jina0924/Plantinum_vol2/Docs/Develop_log_server.md

# 서버 개발 일지

### 2022-08-05

##### [BE] 배포서버 구축 테스트
- 더미 장고 파일을 uwsgi를 사용해서 연결 확인
- 실제 어느정도 구현된 파일은 아직 불가능
    - 장고 하나로 했을 때는 연결되지만 프론트와 연결했을 때에는 되지 않는 문제 발생
    - 두가지 가설 : 포트 번호가 열려있지 않은 것 vs 가상환경
    - localhost:8000 으로 연결이 안된다는 에러메세지 => 장고 runserver 도 안되긴함
    - 프론트에 연결된 주소도 한번 봐야함
    - 다음에 포트번호 상황 여쭈어보기
    - 정안되면 Gunicorn 알아보기
