jina0924/Plantinum_vol2/Docs/[A109] 중간발표.pdf

### 서울 1반 A109

김유민 문요성 이지수 임진경 정진아

# Plantinum

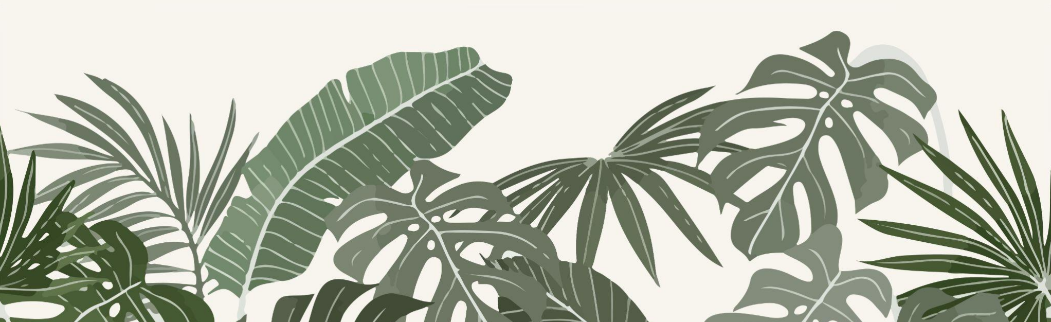
[picture p21: figure]

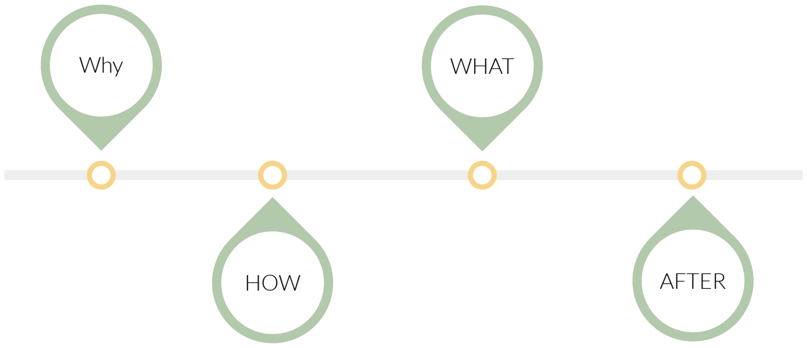
[picture p22: figure]
Why; HOW; WHAT; AFTER

HOW

WHAT

WHY

# CONTENTS

AFTER

# Why?

# WHY?

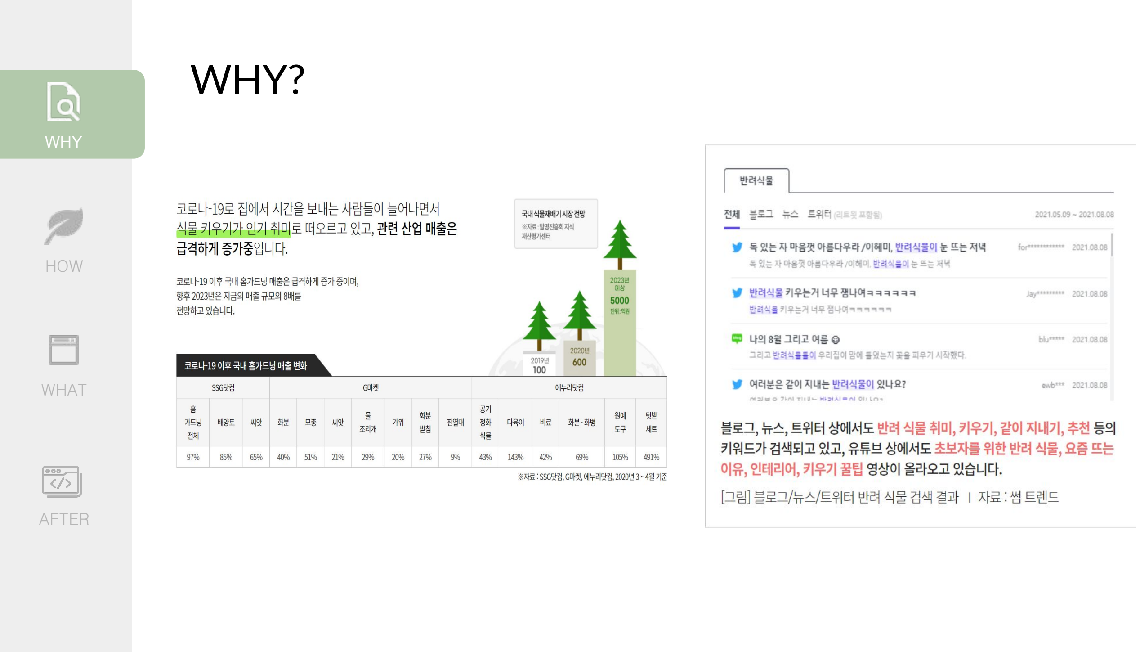
[picture p23: page 4]

WHY

HOW

WHAT

AFTER

# How?

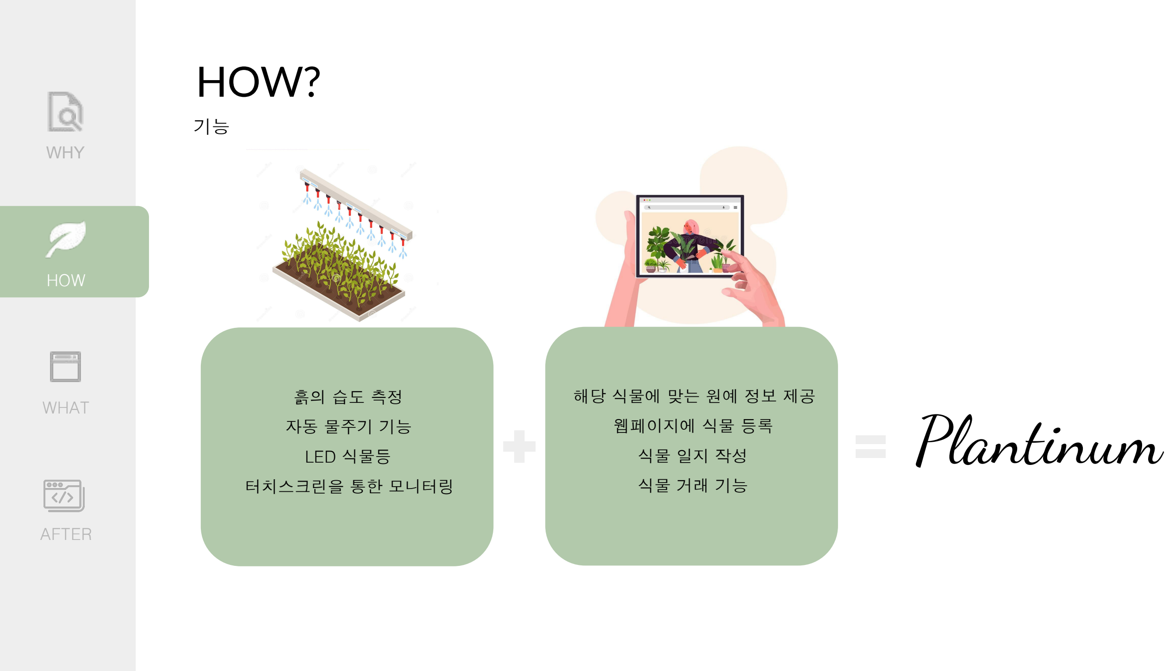
[picture p24: figure]
HOW; HOW?; 자동 물주기 기능; LED 식물등; 터치스크린을 통한 모니터링; 해당 식물에 맞는 원예 정보 제공; 웹페이지에 식물 등록; WHAT; WHY; AFTER; Plantinum

# What?

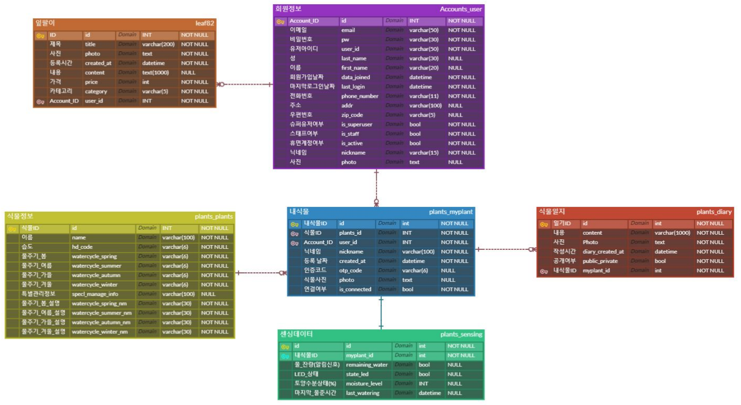
[picture p25: figure]

WHAT

# WHAT

HOW

WHY

AFTER

# WHAT

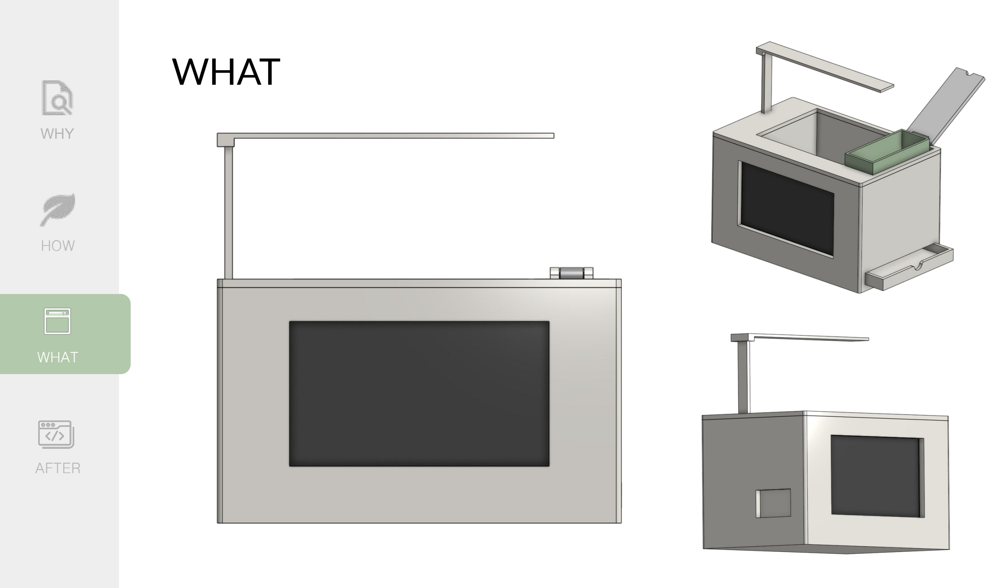
[picture p26: page 9]

WHAT

HOW

WHY

AFTER

## 신규 등록

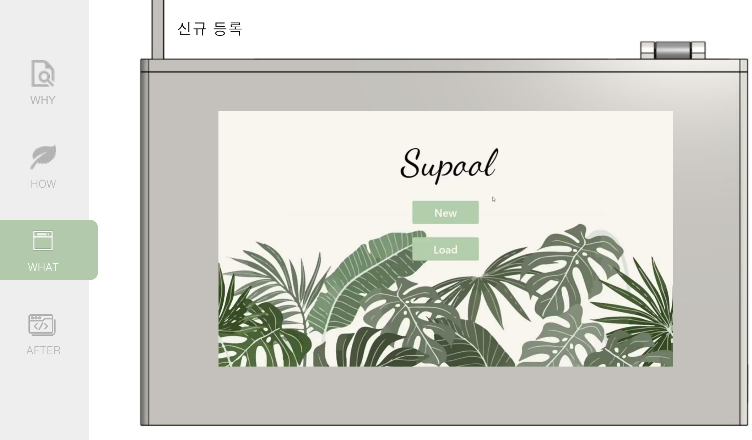
[picture p27: page 10]

WHAT

HOW

WHY

AFTER

## 기존정보 불러오기

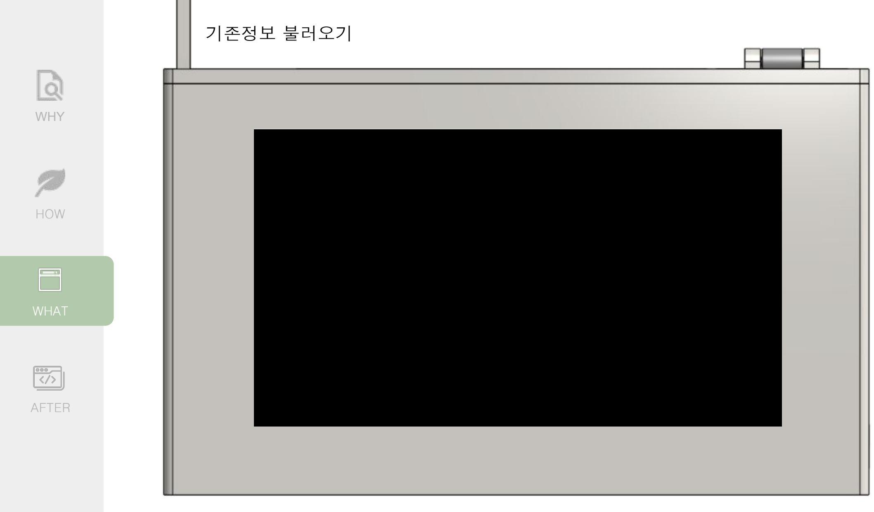
[picture p28: page 11]

WHAT

HOW

WHY

AFTER

# WHAT

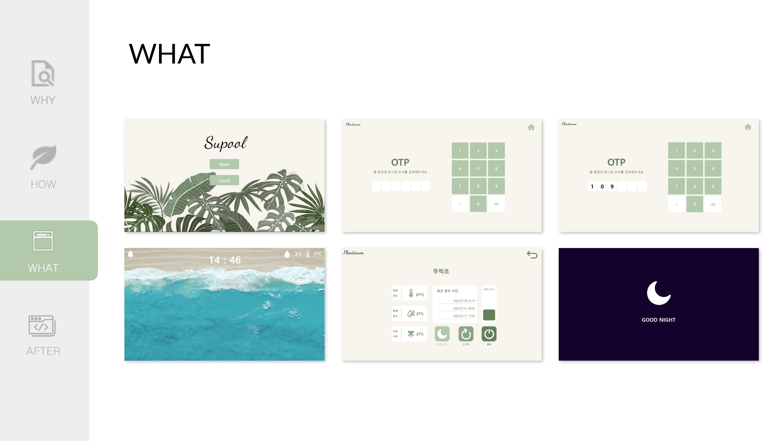
[picture p29: page 12]

WHAT

HOW

WHY

AFTER

# WHAT

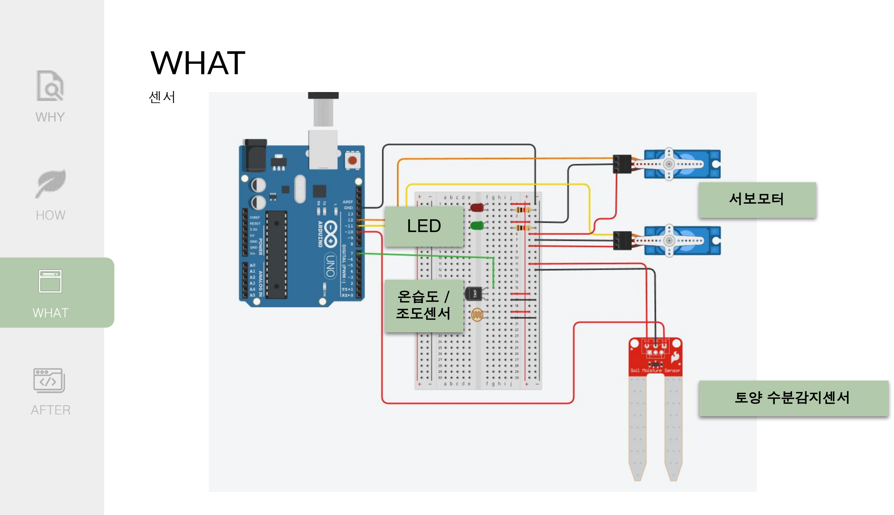
[picture p30: page 13]

센서

서보모터

토양 수분감지센서

## LED

온습도 /
WHAT | 조도센서

HOW

WHY

AFTER

# WHAT

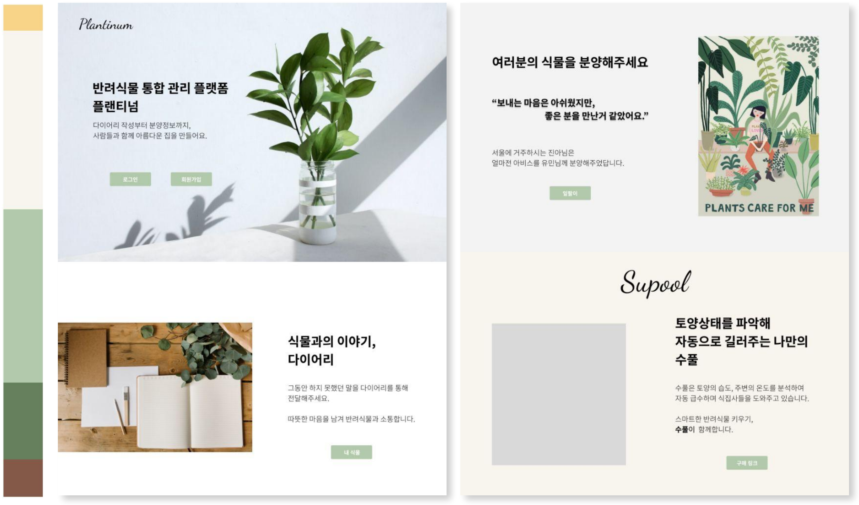
[picture p31: figure]

WHAT

HOW

WHY

AFTER

# WHAT

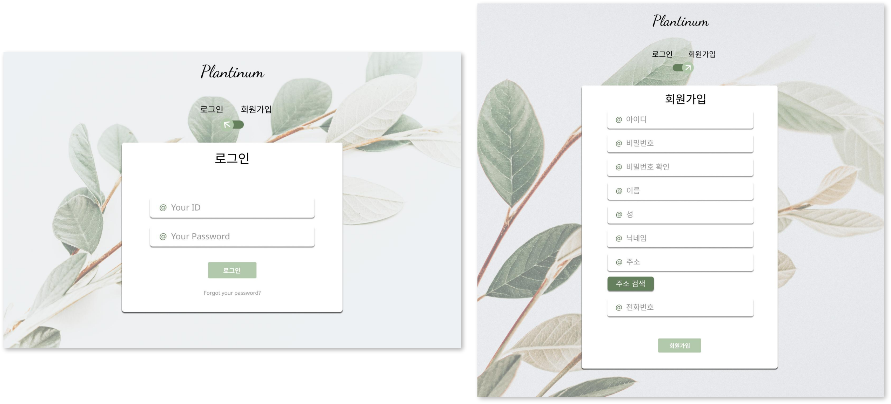
[picture p32: figure]

WHAT

HOW

WHY

AFTER

# WHAT

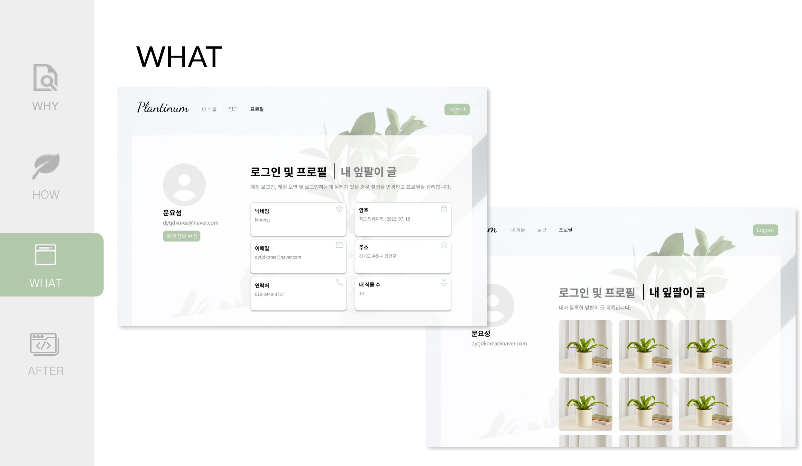
[picture p33: page 16]

WHAT

HOW

WHY

AFTER

# WHAT

WHAT

HOW

WHY

AFTER

## (시연 영상)

# After?

# AFTER

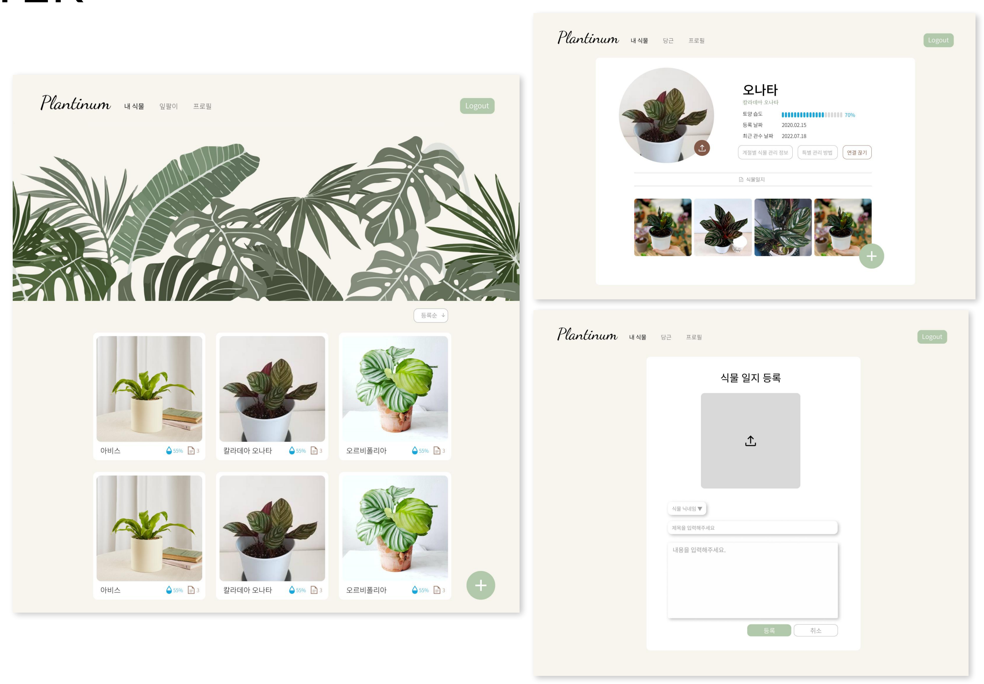
[picture p34: figure]

HOW

WHY

AFTER

WHAT

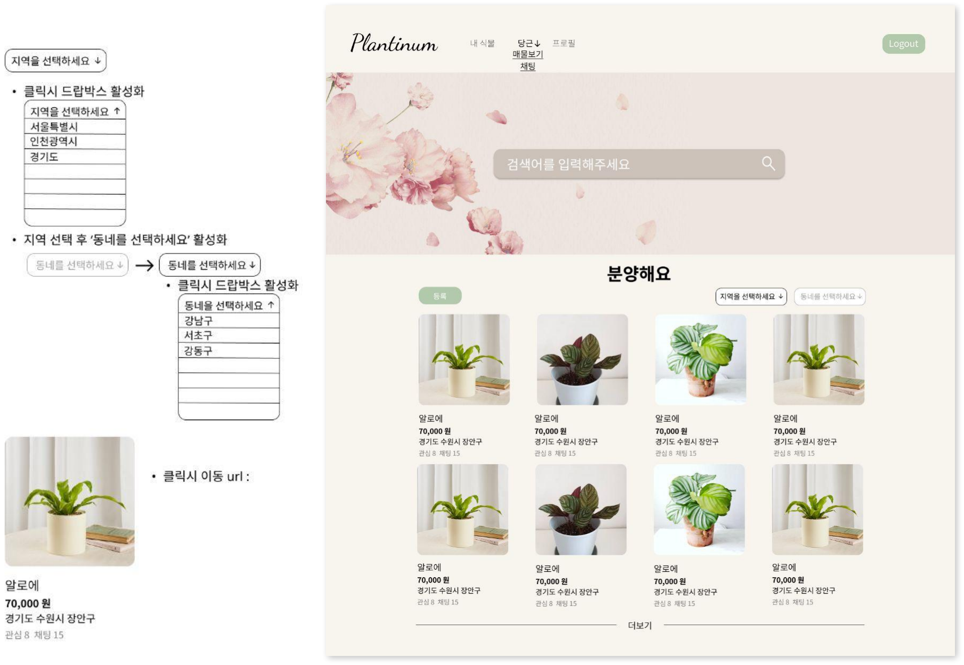
[picture p35: figure]

HOW

WHY

AFTER

WHAT

# AFTER

# AFTER

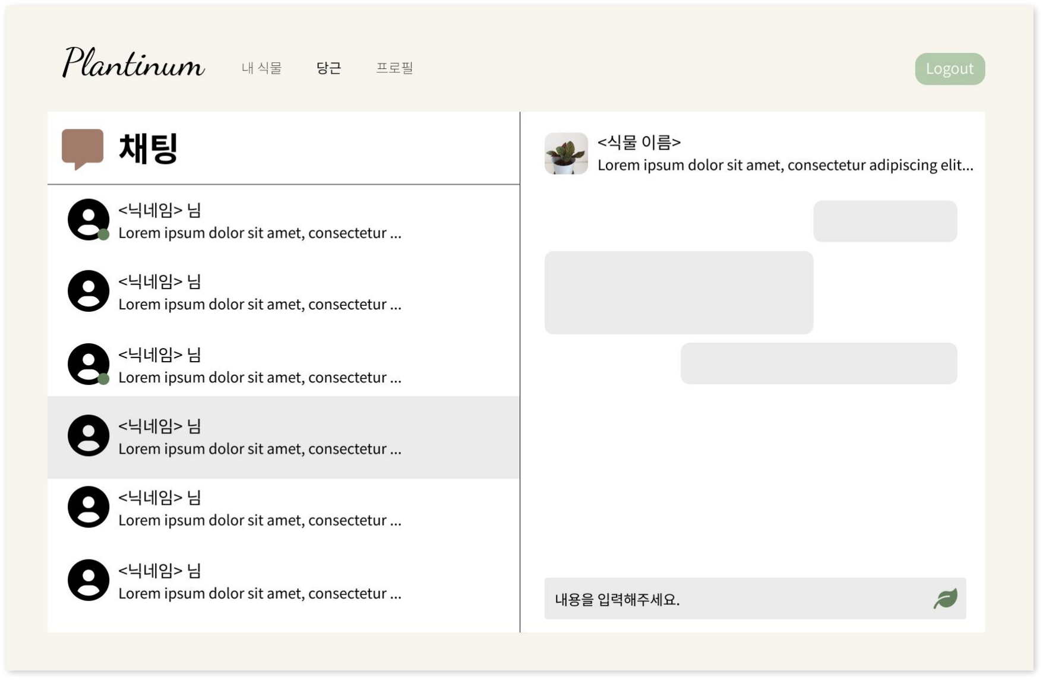
[picture p36: figure]

HOW

WHY

AFTER

WHAT

# Plantinum

Q&A
