jina0924/Plantinum_vol2/exec/공통PJT_서울1반_A109_시연시나리오.pdf

※ 이미 플랜티넘 서비스에 대해 아는 사용자라는 가정 하에 시연 ※ 화면 공유는 전체화면으로

(도입부)

- 플랜테리어 해 놓은 카페에서 본 식물을 내 방에도 두고 싶어 식물을 분양받고자 함
- ex) 마삭줄

(메인 페이지 > 잎팔이)

ㄴㅇㄹ

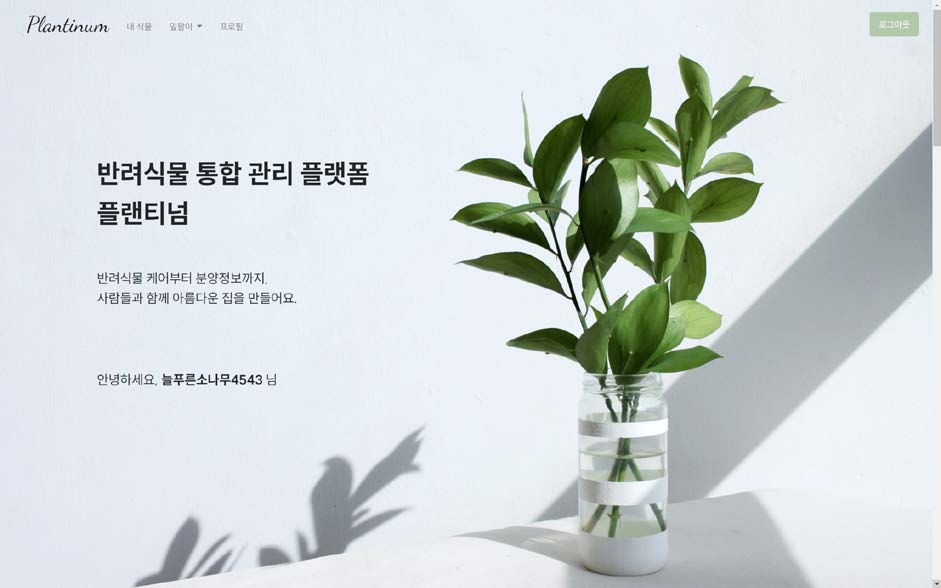
[picture p37: figure]

- plantinum.co.kr 을 통하여 접속
- 잎팔이에 여러 식물이 거래된다는 사실을 알고 있음
- 너무 많은 식물이 있어서 내가 원하는 식물을 찾기 어려움
- 검색을 통해 원하는 식물을 찾아감

## 1. 검색창에 마삭줄 입력

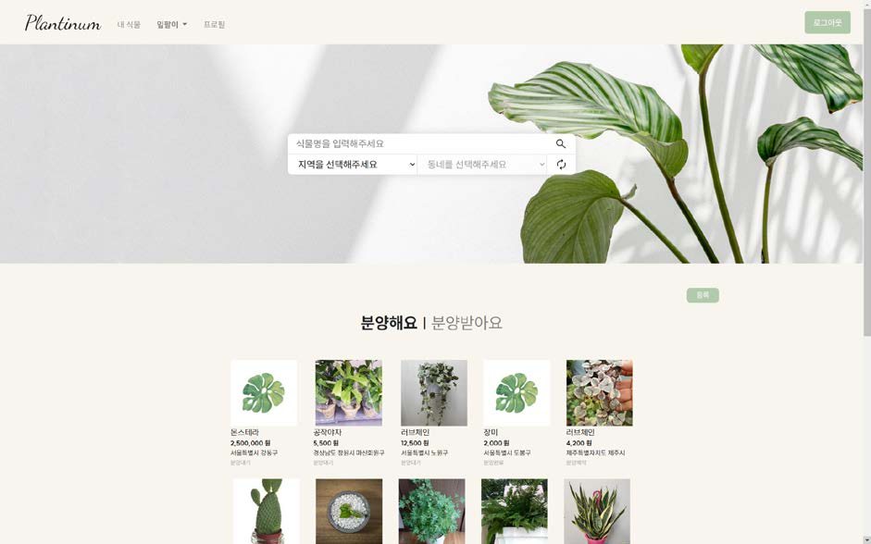
[picture p38: figure]

## 2. 여러 지역의 마삭줄이 나옴

- 사전에 여러 마삭줄 데이터 있어야 함

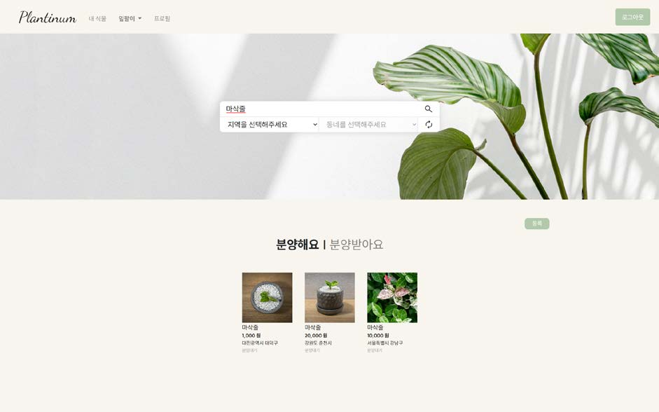
[picture p39: figure]

## 3. 내 근처 지역의 분양 글이 있는지 확인 후 클릭

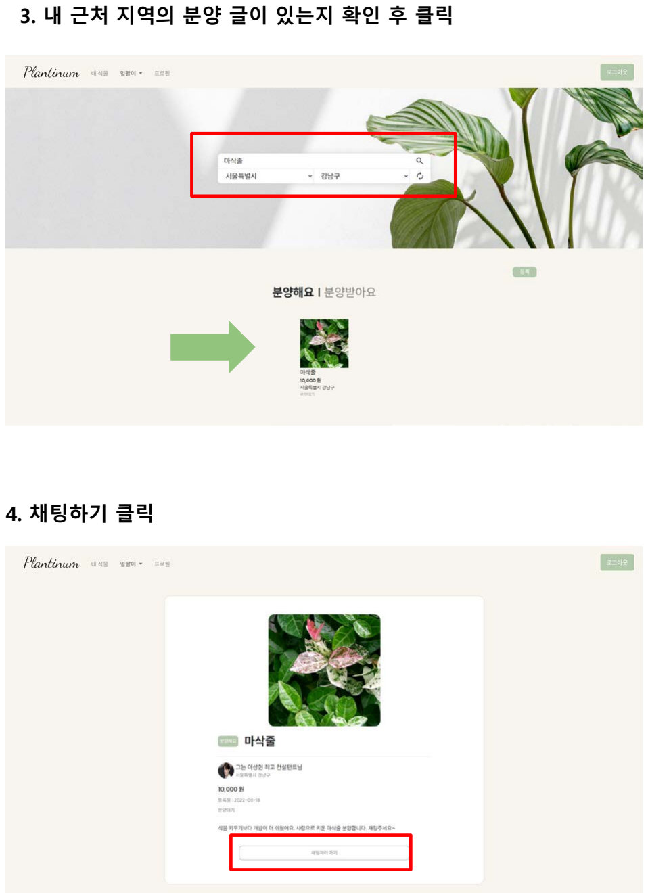
[picture p40: page 4]

## 4. 채팅하기 클릭

ㄴㅇㄹㄴㅇㄹ

## 5. 채팅방 입장

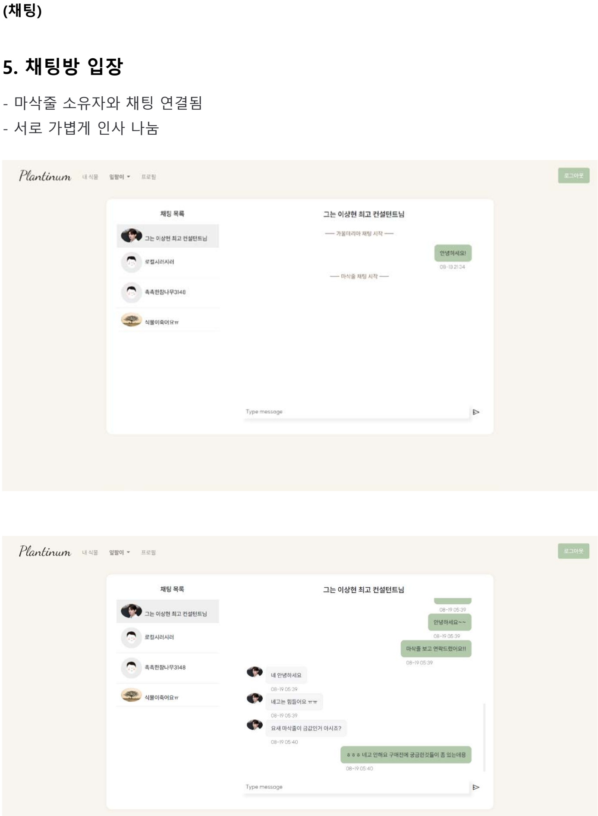
[picture p41: page 5]

(채팅)

- 마삭줄 소유자와 채팅 연결됨
- 서로 가볍게 인사 나눔

## 6. 자유로운 채팅

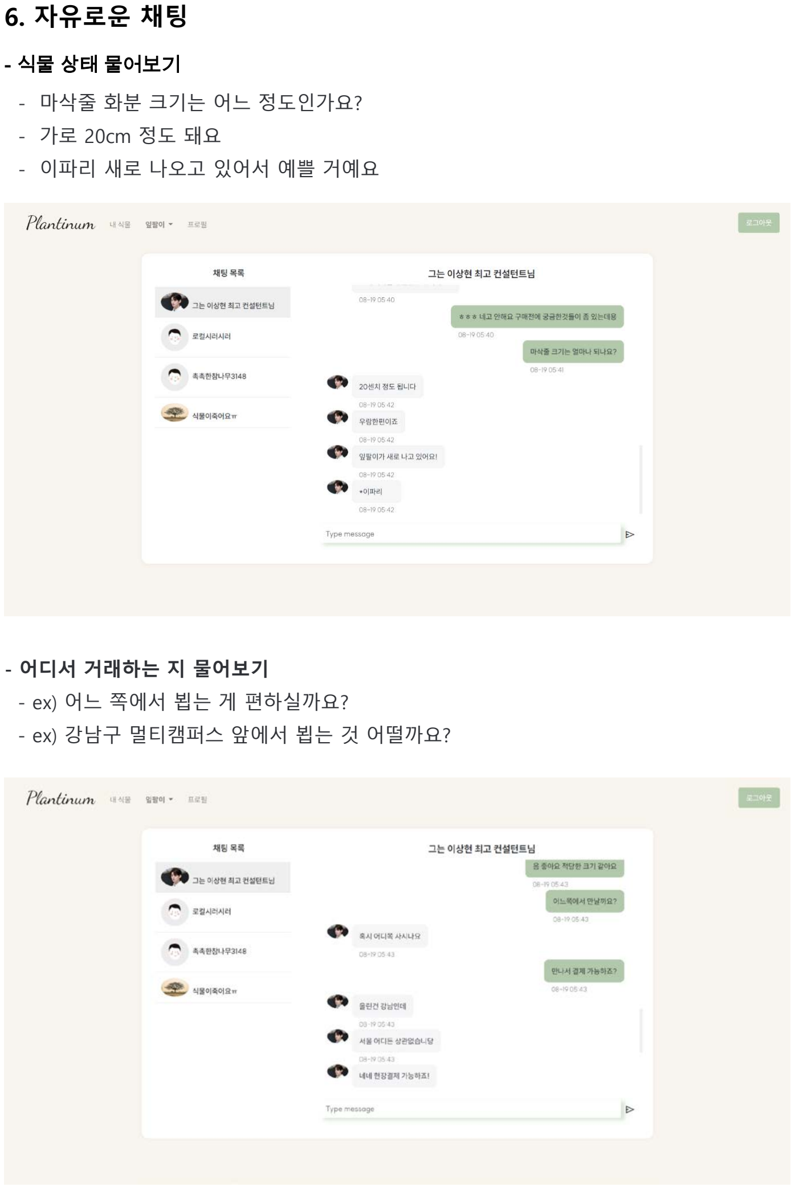
[picture p42: page 6]

### - 식물 상태 물어보기

- 마삭줄 화분 크기는 어느 정도인가요?
- 가로 20cm 정도 돼요
- 이파리 새로 나오고 있어서 예쁠 거예요
- 어디서 거래하는 지 물어보기
- ex) 어느 쪽에서 뵙는 게 편하실까요?
- ex) 강남구 멀티캠퍼스 앞에서 뵙는 것 어떨까요?

- 언제 거래할 지 물어보기
- ex) 편하신 시간 있으면 말씀해주세요
- ex) 6시에 괜찮으신가요?
- ex) 네 그럼 6시 멀캠 앞에서 만나요~

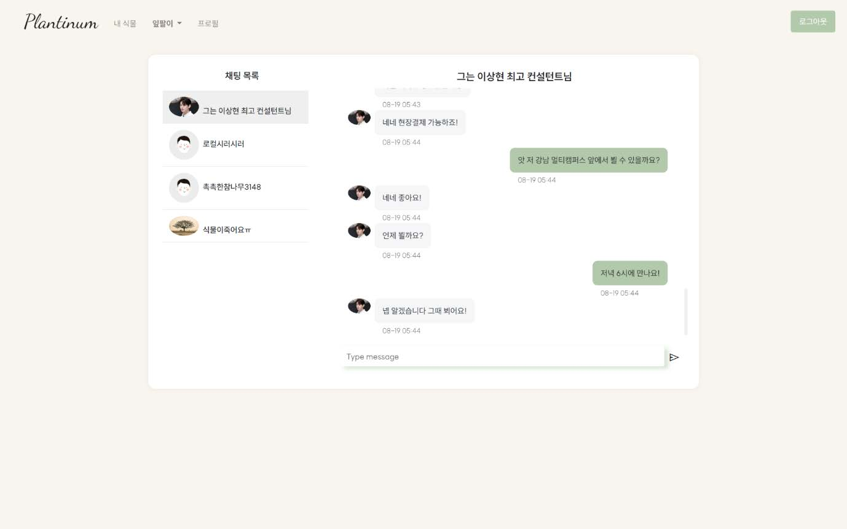
[picture p43: figure]

(내식물)

## 7. 사온 마삭줄 등록하기

- 식물 닉네임 = 금쪽이
- 식물 종류 = 마삭줄
- 식물 종류 검색할 때 마삭까지만 검색해서 연관 리스트 띄워주기
- 등록 클릭

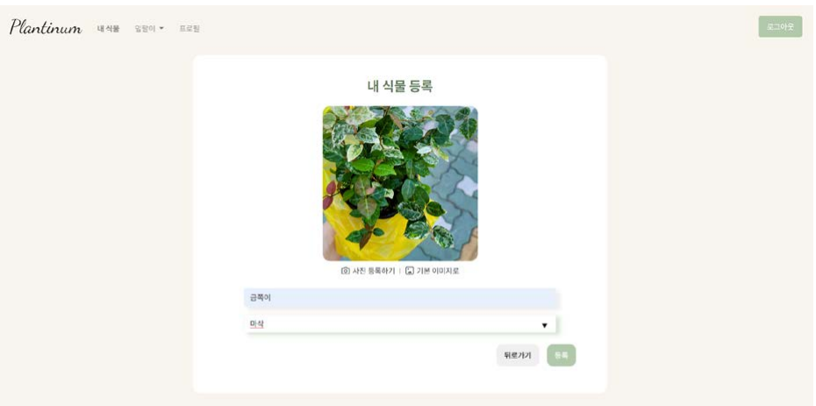
[picture p44: figure]
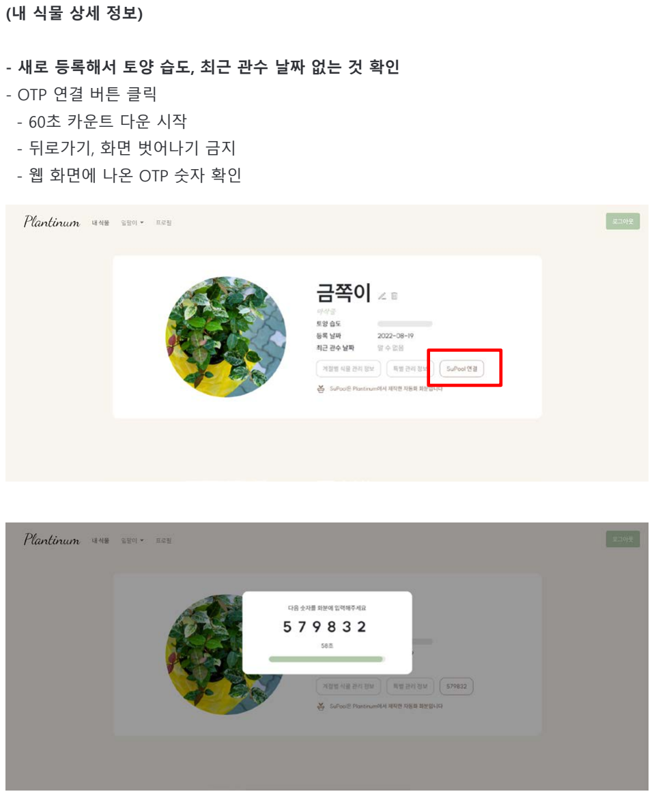
[picture p45: page 9]

(내 식물 상세 정보)

- 새로 등록해서 토양 습도, 최근 관수 날짜 없는 것 확인
- OTP 연결 버튼 클릭
- 60초 카운트 다운 시작
- 뒤로가기, 화면 벗어나기 금지
- 웹 화면에 나온 OTP 숫자 확인

## 8. SuPool 연결

(핸드폰 화면 공유)
- 웹 화면에서 본 숫자 SuPool에 연결
- 핸드폰 카메라로 OTP 숫자 입력하는 부분 자세히 보여주기
- SuPool 작동 후 new 클릭으로 식물등록페이지 이동

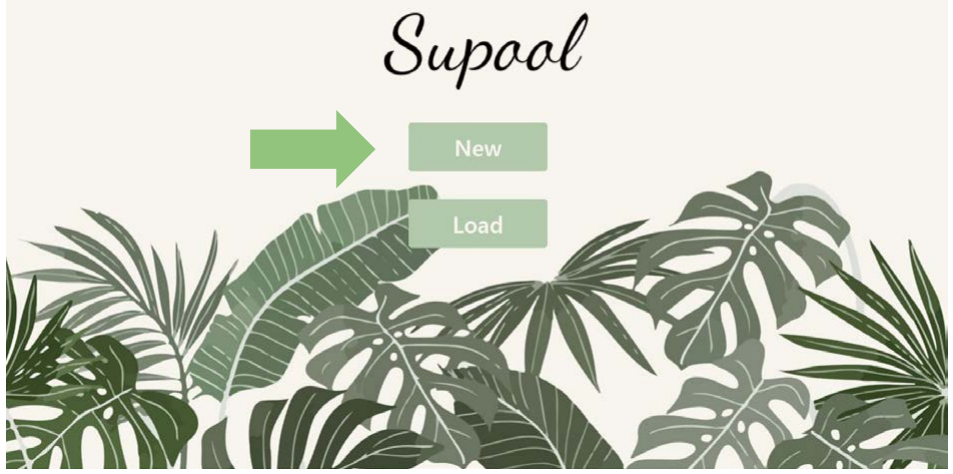
[picture p46: figure]
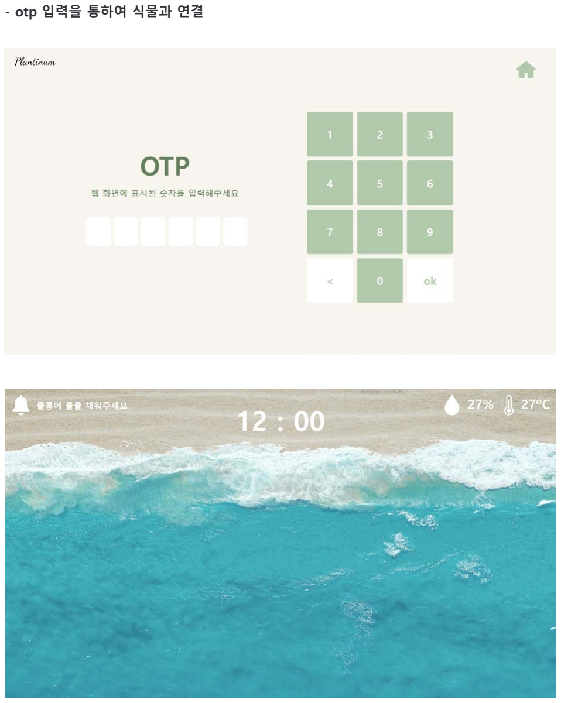
[picture p47: page 11]

- otp 입력을 통하여 식물과 연결

(내 식물 상세 정보)

- OTP 연결되어 모달 창 내려갈 것
- 토양 수분 정도 측정된 값 확인하기

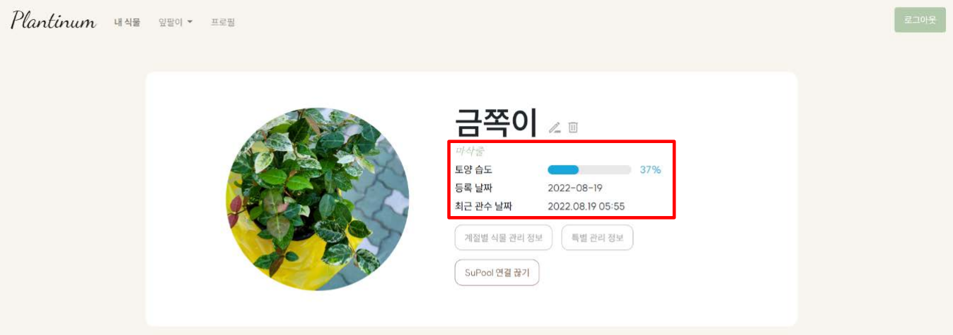
[picture p48: figure]
