jina0924/Plantinum_vol2/FE/plantinum/src/assets/HomeView/background_img.jpg

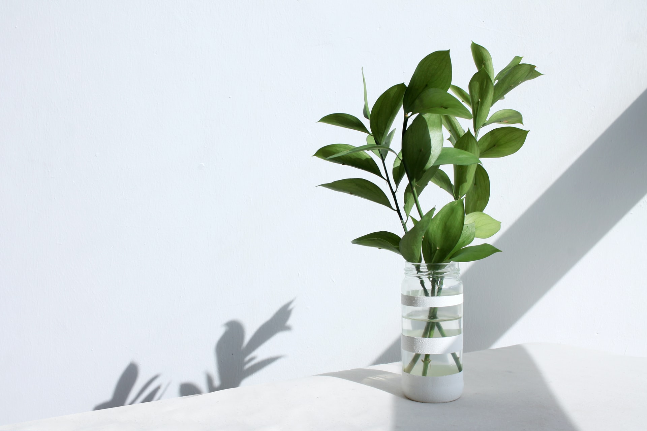
FE/plantinum/src/assets/HomeView/background_img.jpg
