jina0924/Plantinum_vol2/FE/plantinum/src/assets/HomeView/main_pic_1.jpg

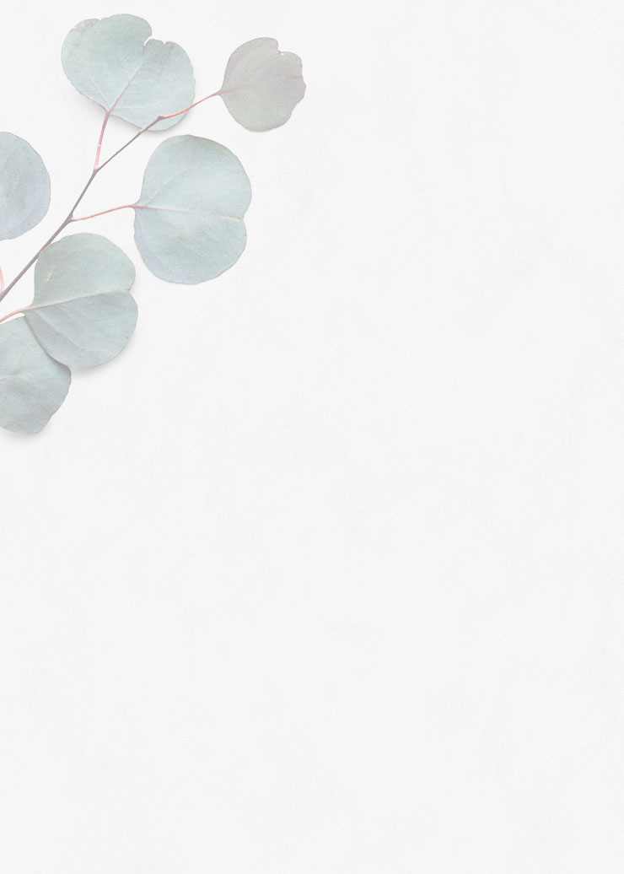
FE/plantinum/src/assets/HomeView/main_pic_1.jpg
