jina0924/Plantinum_vol2/FE/plantinum/src/assets/HomeView/main_pic_3.jpg

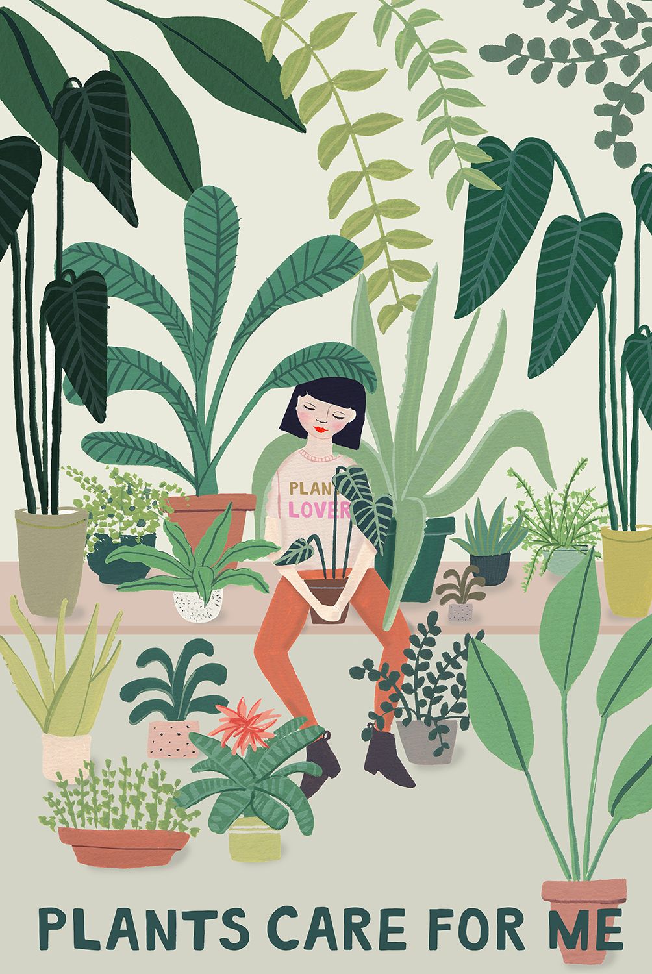
FE/plantinum/src/assets/HomeView/main_pic_3.jpg
