jina0924/Plantinum_vol2/FE/plantinum/src/assets/Leaf82/searchbar_pic_0.jpg

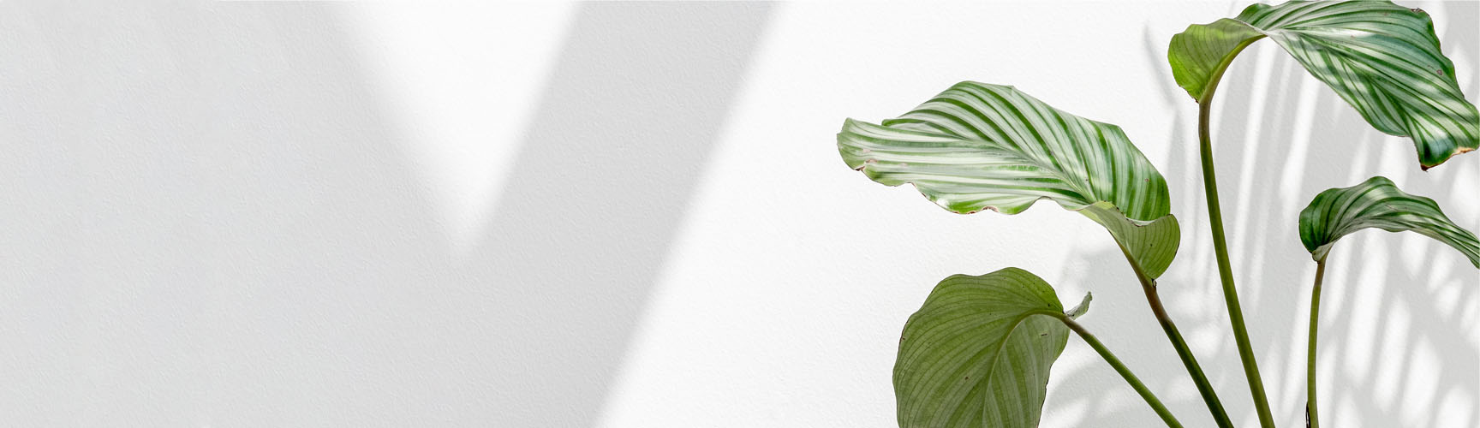
FE/plantinum/src/assets/Leaf82/searchbar_pic_0.jpg
