jina0924/Plantinum_vol2/FE/plantinum/src/assets/Login/login_bg.jpg

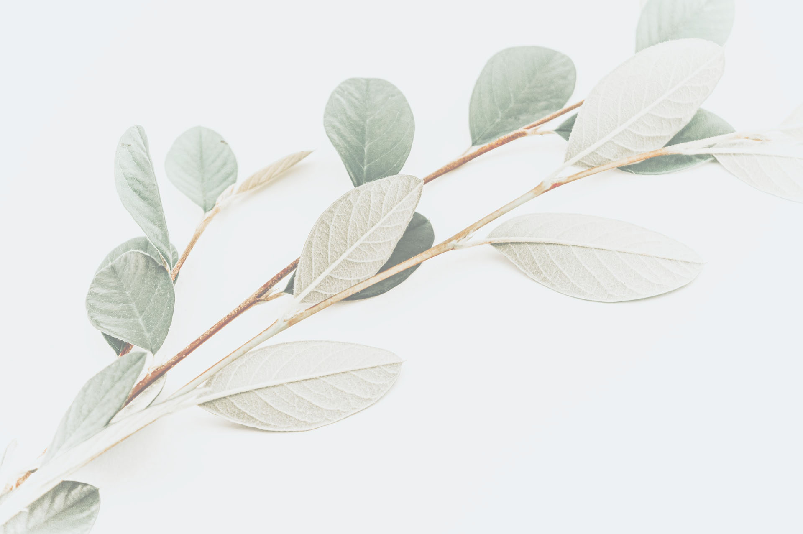
FE/plantinum/src/assets/Login/login_bg.jpg
