jina0924/Plantinum_vol2/HW/LCD_img/background_supool.jpg

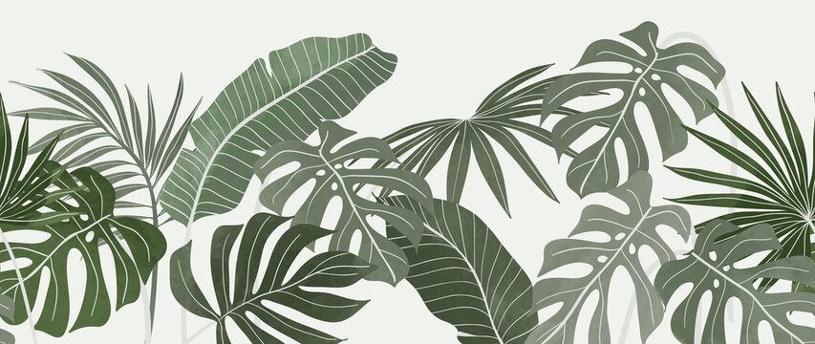
HW/LCD_img/background_supool.jpg
