jina0924/Plantinum_vol2/HW/RP2/img_element/SPOOL_3.png

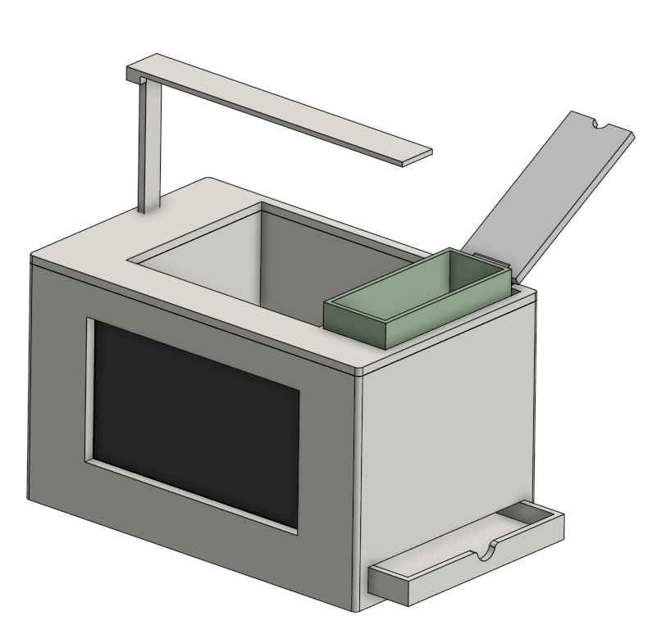
HW/RP2/img_element/SPOOL_3.png
