jina0924/Plantinum_vol2/HW/Supool/img/background_sand.jpg

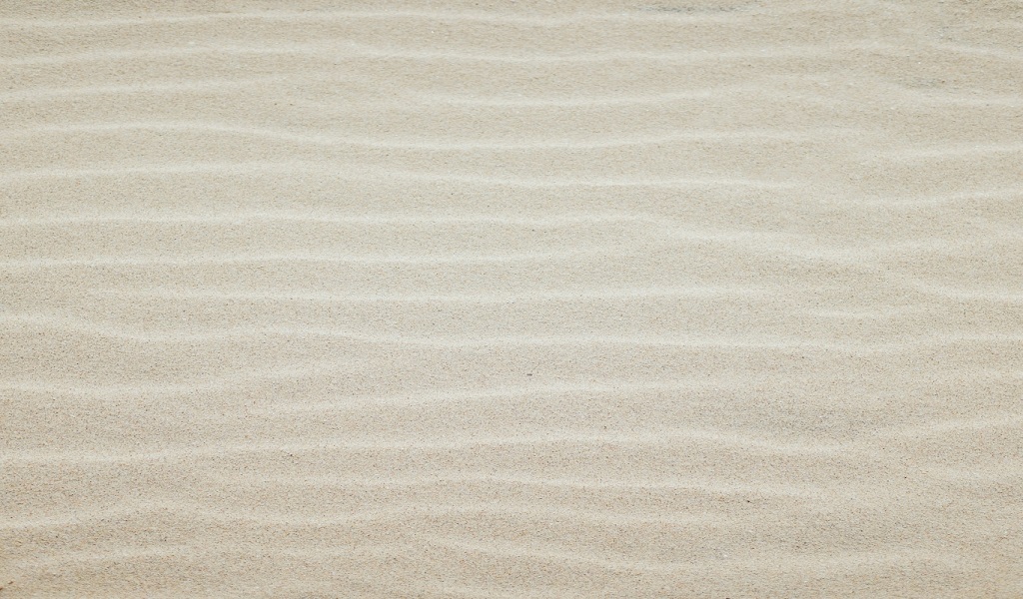
HW/Supool/img/background_sand.jpg
