jina0924/Plantinum_vol2/HW/Supool/img/bell_white.png

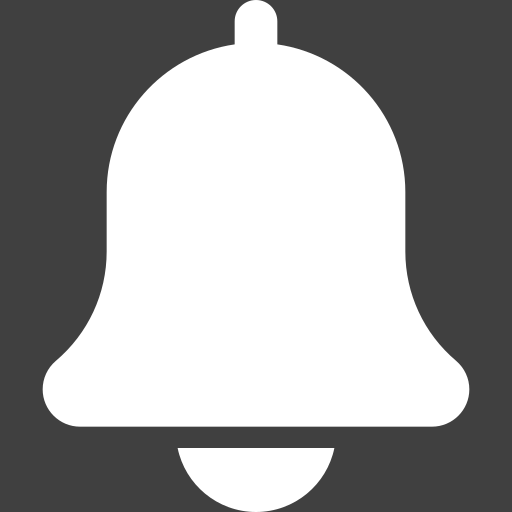
HW/Supool/img/bell_white.png
