jina0924/Plantinum_vol2/HW/Supool/img/humidity_white.png

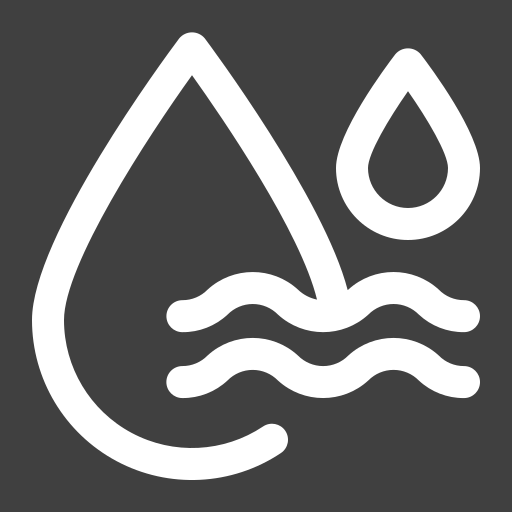
HW/Supool/img/humidity_white.png
