jina0924/Plantinum_vol2/HW/Supool/img/icc_background_sand.png

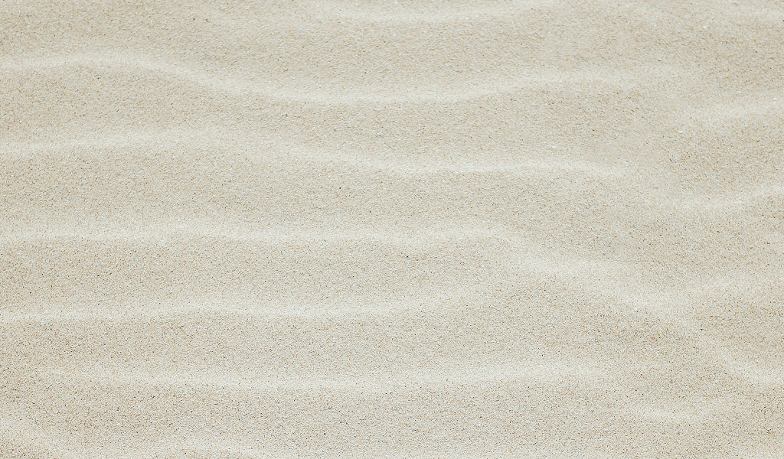
HW/Supool/img/icc_background_sand.png
