jina0924/Plantinum_vol2/HW/Supool/img/ocean.jpg

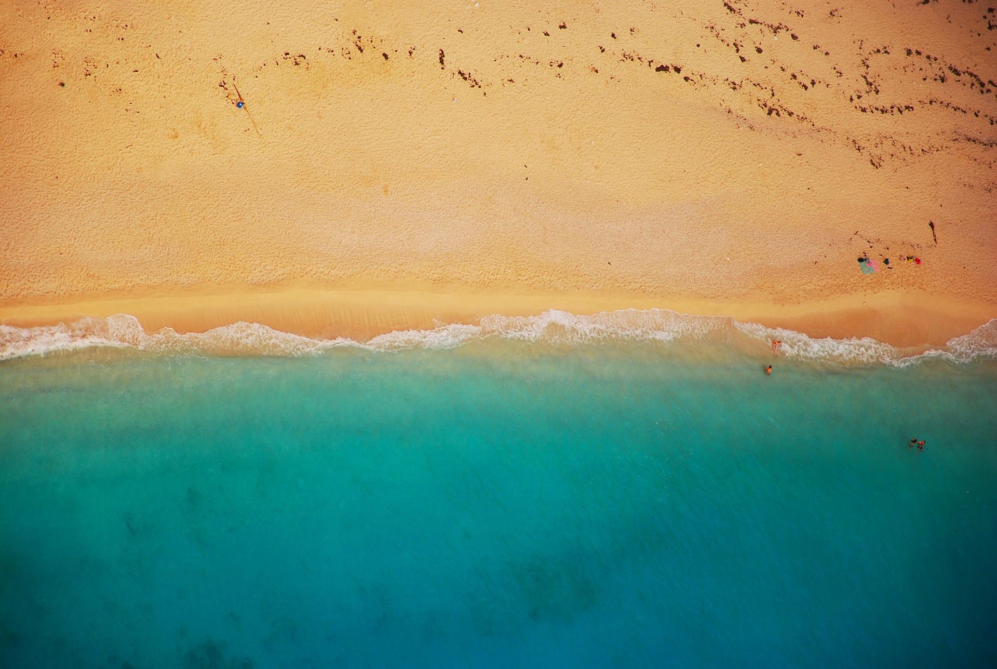
HW/Supool/img/ocean.jpg
