jina0924/Plantinum_vol2/HW/Supool/img/power-off.png

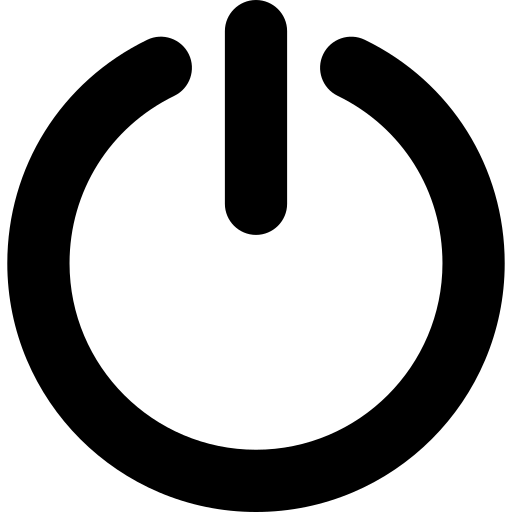
HW/Supool/img/power-off.png
