jina0924/Plantinum_vol2/HW/Supool/img/redo.png

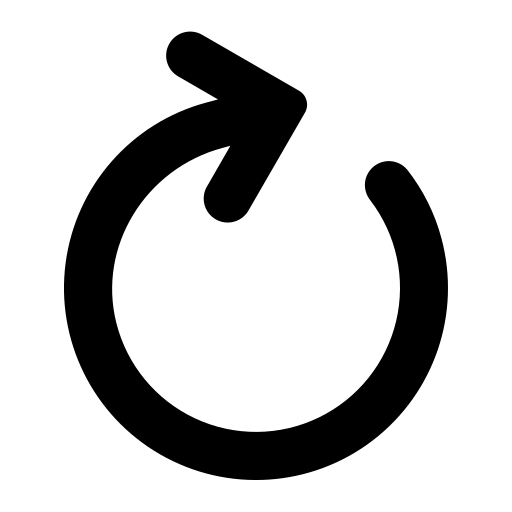
HW/Supool/img/redo.png
