jina0924/Plantinum_vol2/HW/Supool/img/temperature_white.png

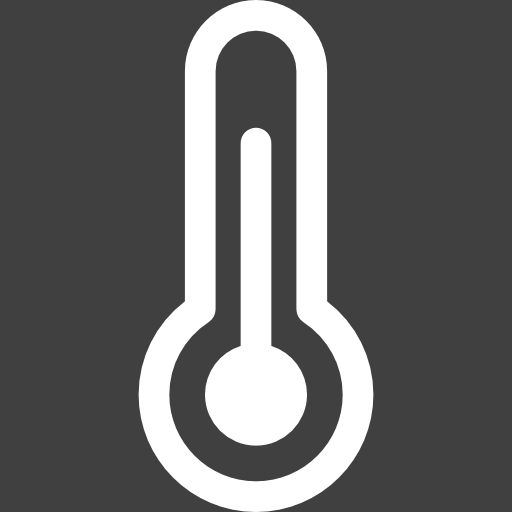
HW/Supool/img/temperature_white.png
