jina0924/Plantinum_vol2/HW/Supool/img/water.png

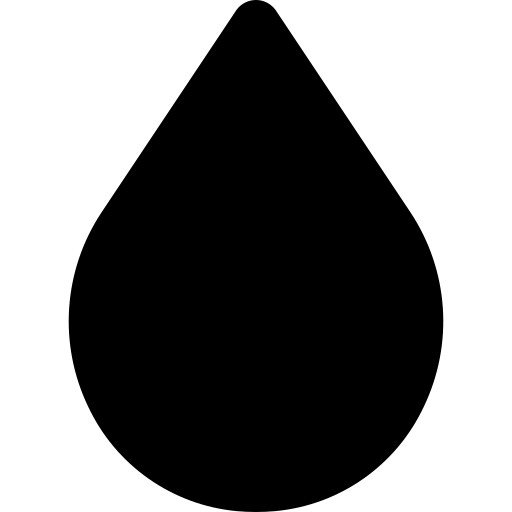
HW/Supool/img/water.png
