jina0924/Plantinum_vol2/README.assets/1.png

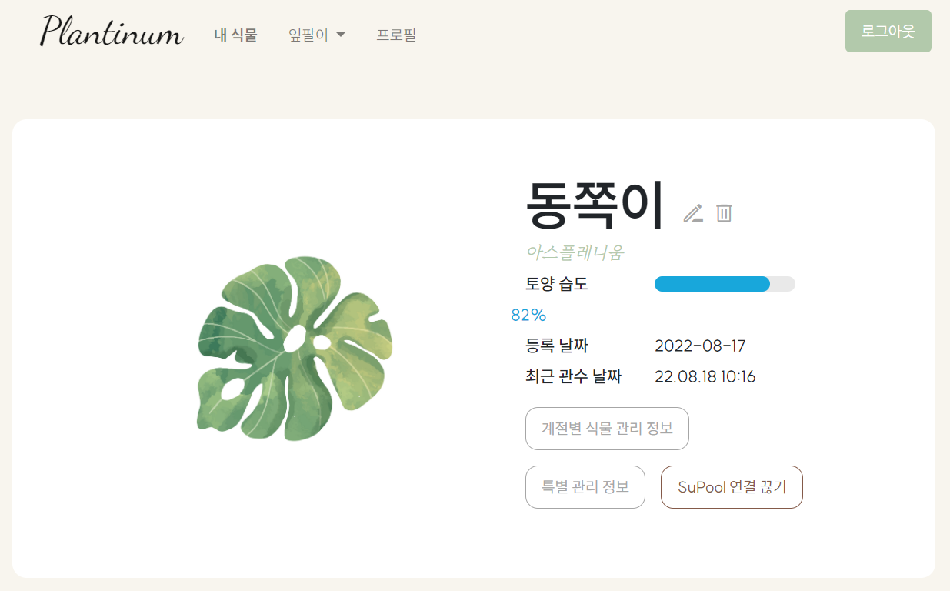
README.assets/1.png
