jina0924/Plantinum_vol2/README.assets/2.png

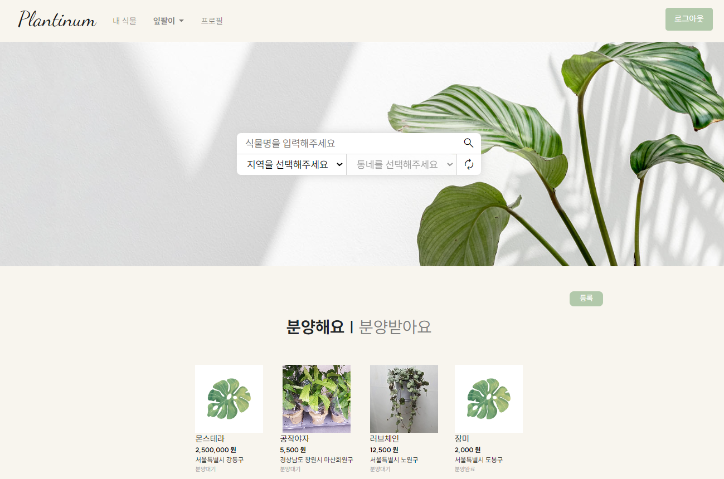
README.assets/2.png
