jina0924/Plantinum_vol2/HW/RP1/sensor_test/AduinoUno/WaterPump/WaterPump.ino

int AA = 13;  // AA를 연결한 디지털 핀
int AB = 10;   // AB를 연결한 디지털 핀
 
void setup()
{
  pinMode(AA, OUTPUT);  // AA를 출력 핀으로 설정
  pinMode(AB, OUTPUT);  // AB를 출력 핀으로 설정
}
 
void loop()
{
  digitalWrite(AA, HIGH);  // 정방향으로 모터 회전
  digitalWrite(AB, LOW);
  delay(5000);  // 5초동안 상태 유지(1000ms = 5s)
 
  digitalWrite(AA, LOW);  // 모터 정지
  digitalWrite(AB, LOW);
  delay(5000);  // 5초동안 상태 유지(1000ms = 5s)
}
